AethelVeritas/Fulmen/PCB/Fulmen.kicad_sch

## KiCad design PCB/Fulmen.kicad_sch (2025-08-24)

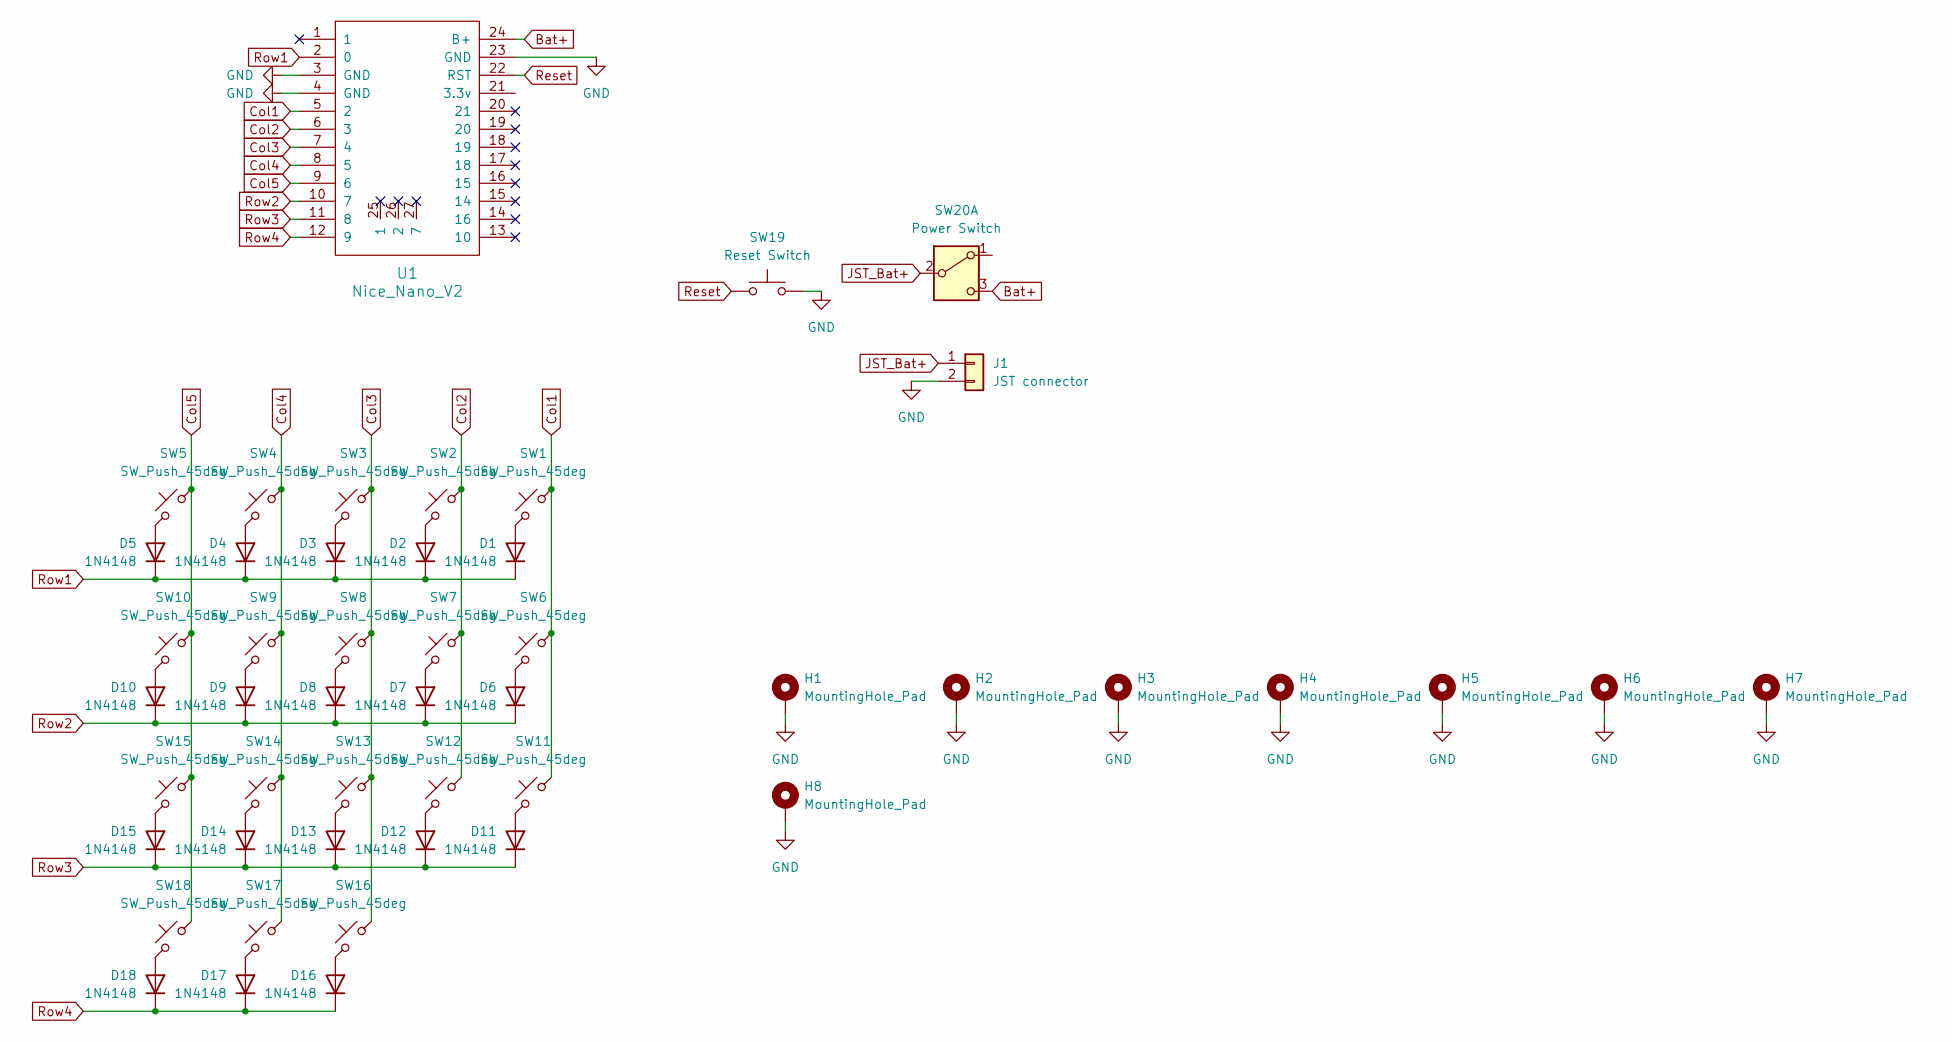
[picture p5: schematic Fulmen.kicad_sch]

Parts:
D1, D2, D3, D4, D5, D6, D7, D8, D9, D10, D11, D12, D13, D14, D15, D16, D17, D18: 1N4148; 1N4148 Cutout Diode
H1, H2, H3, H4, H5, H6, H7, H8: MountingHole_Pad; MountingHole_2.2mm_M2_DIN965_Pad
J1: JST connector; Connector_1x02_JST-PH
SW1, SW2, SW3, SW4, SW5, SW6, SW7, SW8, SW9, SW10, SW11, SW12, SW13, SW14, SW15, SW16, SW17, SW18: SW_Push_45deg
SW19: Reset Switch; SW_SPST_B3U-1000P_Reversible
SW20: Power Switch; SW_MSK12C02-HB_Reversible
U1: Nice_Nano_V2

Connections:
Bat+: SW20.3 (C), U1.24 (B+)
Col1: SW1.1, SW6.1, SW11.1, U1.5 (2)
Col2: SW2.1, SW7.1, SW12.1, U1.6 (3)
Col3: SW3.1, SW8.1, SW13.1, SW16.1, U1.7 (4)
Col4: SW4.1, SW9.1, SW14.1, SW17.1, U1.8 (5)
Col5: SW5.1, SW10.1, SW15.1, SW18.1, U1.9 (6)
GND: H1.1, H2.1, H3.1, H4.1, H5.1, H6.1, H7.1, H8.1, J1.2, SW19.2, U1.3 (GND), U1.4 (GND), U1.23 (GND)
JST_Bat+: J1.1, SW20.2 (B)
unnamed: D1.2 (A), SW1.2
unnamed: D2.2 (A), SW2.2
unnamed: D3.2 (A), SW3.2
unnamed: D4.2 (A), SW4.2
unnamed: D5.2 (A), SW5.2
unnamed: D6.2 (A), SW6.2
unnamed: D7.2 (A), SW7.2
unnamed: D8.2 (A), SW8.2
unnamed: D9.2 (A), SW9.2
unnamed: D10.2 (A), SW10.2
unnamed: D11.2 (A), SW11.2
unnamed: D12.2 (A), SW12.2
unnamed: D13.2 (A), SW13.2
unnamed: D14.2 (A), SW14.2
unnamed: D15.2 (A), SW15.2
unnamed: D16.2 (A), SW16.2
unnamed: D17.2 (A), SW17.2
unnamed: D18.2 (A), SW18.2
Reset: SW19.1, U1.22 (RST)
Row1: D1.1 (K), D2.1 (K), D3.1 (K), D4.1 (K), D5.1 (K), U1.2 (0)
Row2: D6.1 (K), D7.1 (K), D8.1 (K), D9.1 (K), D10.1 (K), U1.10 (7)
Row3: D11.1 (K), D12.1 (K), D13.1 (K), D14.1 (K), D15.1 (K), U1.11 (8)
Row4: D16.1 (K), D17.1 (K), D18.1 (K), U1.12 (9)
